raducosminalexandru/EbookReader/Images/2.png

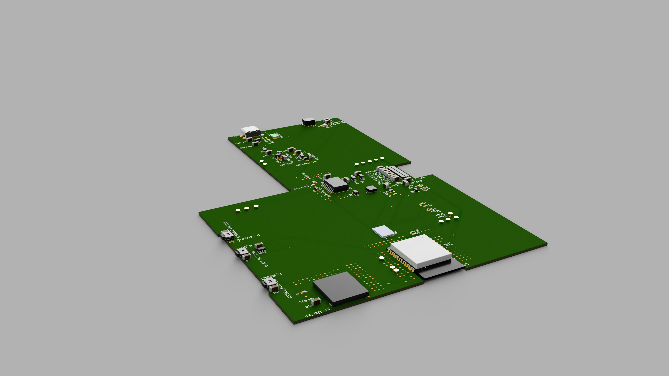
Images/2.png
