raducosminalexandru/EbookReader/Images/3.png

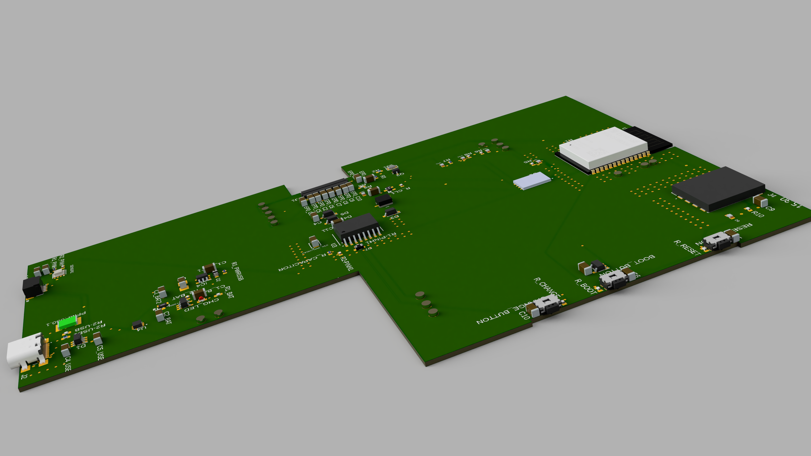
Images/3.png
