raducosminalexandru/EbookReader/Images/4.png

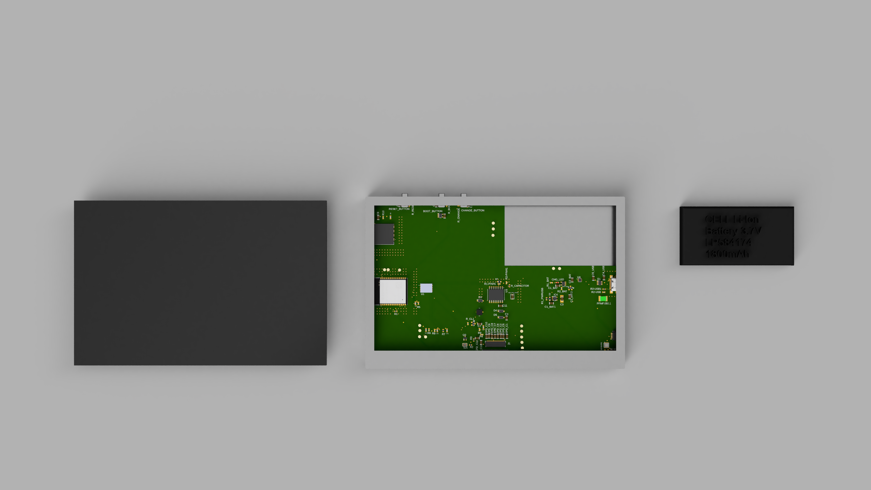
Images/4.png
