raducosminalexandru/EbookReader/Images/5.png

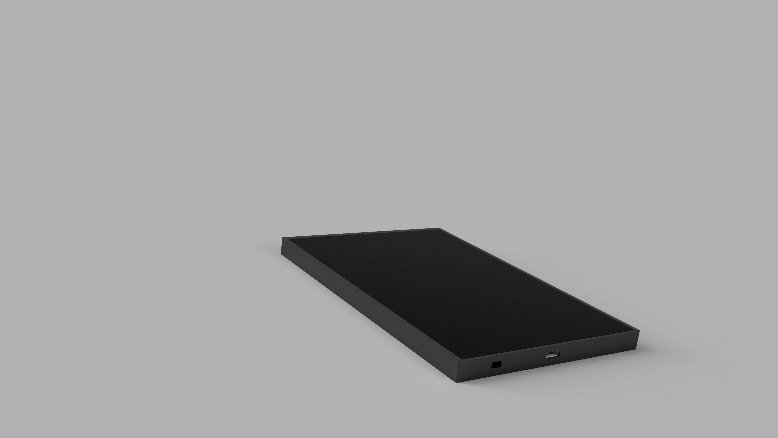
Images/5.png
