raducosminalexandru/EbookReader/Images/6.png

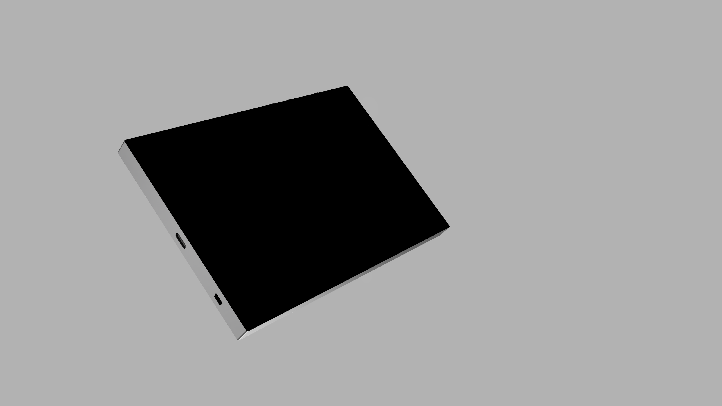
Images/6.png
