raducosminalexandru/EbookReader/Images/7.png

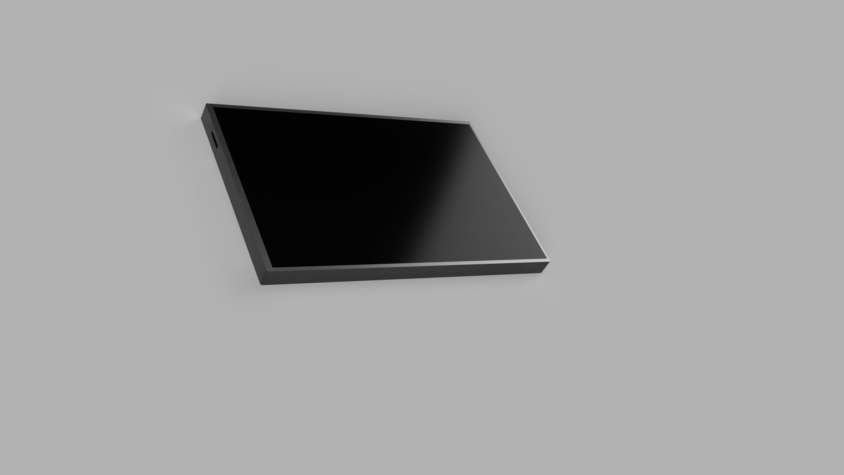
Images/7.png
