raducosminalexandru/EbookReader/Images/8.png

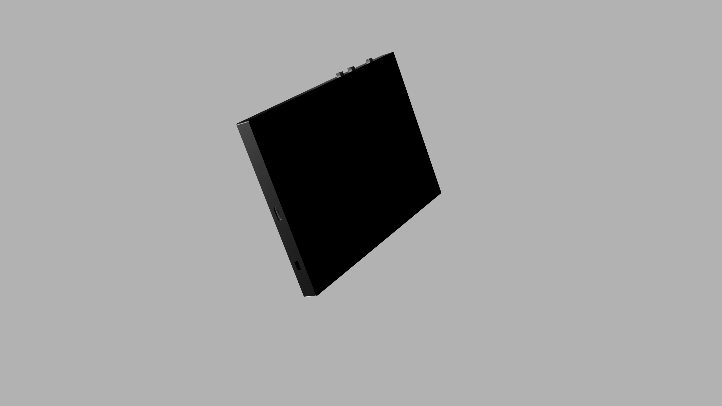
Images/8.png
